gfoudree/TOTPVault/totpvault-cli/src/tests.rs

#[cfg(test)]
mod tests {
    use crate::comm::send_message;
    use crate::dev::DEFAULT_UART_DELAY;
    use crate::{comm::check_status_msg, dev::TotpvaultDev};
    use base64::Engine;
    use base64::prelude::BASE64_STANDARD;
    use chrono::Utc;
    use ed25519_dalek::{Signature, Signer, SigningKey, VerifyingKey};
    use rand_latest::Rng;
    use rand_older::rngs::OsRng;
    use rmp_serde::to_vec;
    use serial_test::serial;
    use std::time;
    use std::{env, thread, time::Duration};
    use totp_rs::{Secret, TOTP};
    use totpvault_lib::{
        AUTO_VAULT_LOCK_SECONDS, AUTOLOCK_OFF, AUTOLOCK_ON, AuthenticateChallengeMsg, CMD_ATTEST,
        CreateEntryMsg, MAX_PW_LEN, MSG_STATUS_MSG, Message, SETTING_AUTOLOCK, StatusMsg,
    };

    const TEST_PASSWORD: &str = "password12345!";

    fn init_vault(dev: &String) {
        let valid_pw = TEST_PASSWORD;
        TotpvaultDev::init_vault(&dev, None, valid_pw).unwrap();
    }
    fn unlock_vault(dev: &String) {
        let valid_pw = TEST_PASSWORD;
        TotpvaultDev::unlock_vault(&dev, None, valid_pw).unwrap();
    }

    #[test]
    fn test_public_key_to_hash_invalid_base64() {
        let invalid_public_key = "!!invalid_base64!!";
        assert!(TotpvaultDev::public_key_to_hash(invalid_public_key).is_err());
    }

    #[test]
    fn test_public_key_to_hash_empty_input() {
        let empty_key = "";
        assert!(TotpvaultDev::public_key_to_hash(empty_key).is_err());
    }
    #[test]
    fn test_public_key_to_hash_valid_input() {
        let valid_key = "U29tZVZhbGlkUHVibGljS2V5";
        assert!(TotpvaultDev::public_key_to_hash(valid_key).is_ok());
    }

    #[test]
    fn test_valid_signature() {
        // Generate a signing key
        let mut csprng = OsRng;
        let signing_key = SigningKey::generate(&mut csprng);
        let verifying_key = VerifyingKey::from(&signing_key);

        let message = b"Hello, world!";
        let signature: Signature = signing_key.sign(message);

        // Verify the signature
        let result = TotpvaultDev::ed25519_verify_signature(
            verifying_key.as_bytes(),
            message,
            &signature.to_vec(),
        );

        assert!(result.is_ok());
    }

    #[test]
    fn test_invalid_signature() {
        let mut csprng = OsRng;
        let signing_key = SigningKey::generate(&mut csprng);
        let verifying_key = VerifyingKey::from(&signing_key);

        let message = b"Hello, world!";
        let signature: Signature = signing_key.sign(message);

        // Tampered message
        let tampered_message = b"Hello, rust!";

        let result = TotpvaultDev::ed25519_verify_signature(
            verifying_key.as_bytes(),
            tampered_message,
            &signature.to_vec(),
        );

        assert!(result.is_err());
    }

    #[test]
    fn test_invalid_public_key() {
        let mut csprng = OsRng;
        let signing_key = SigningKey::generate(&mut csprng);

        let message = b"Hello, world!";
        let signature: Signature = signing_key.sign(message);

        // Generate a different keypair
        let different_signing_key = SigningKey::generate(&mut csprng);
        let different_verifying_key = VerifyingKey::from(&different_signing_key);

        let result = TotpvaultDev::ed25519_verify_signature(
            different_verifying_key.as_bytes(),
            message,
            &signature.to_vec(),
        );

        assert!(result.is_err());
    }

    #[test]
    fn test_empty_fields() {
        let empty_field = [0u8; 32];
        let mut csprng = OsRng;
        let signing_key = SigningKey::generate(&mut csprng);
        let verifying_key = VerifyingKey::from(&signing_key);

        let message = b"Hello, world!";
        let signature: Signature = signing_key.sign(message);

        assert!(
            TotpvaultDev::ed25519_verify_signature(
                verifying_key.as_bytes(),
                &empty_field,
                &signature.to_vec()
            )
            .is_err()
        );
        assert!(
            TotpvaultDev::ed25519_verify_signature(&empty_field, message, &signature.to_vec())
                .is_err()
        );
        assert!(
            TotpvaultDev::ed25519_verify_signature(verifying_key.as_bytes(), message, &empty_field)
                .is_err()
        );
    }

    #[test]
    fn test_valid_success_status_msg() {
        let status_msg = StatusMsg {
            error: false,
            message: "Operation successful".to_string(),
        };
        let mut encoded = vec![MSG_STATUS_MSG];
        encoded.extend(to_vec(&status_msg).unwrap());

        let result = check_status_msg(encoded);
        assert!(result.is_ok());
    }

    #[test]
    fn test_valid_error_status_msg() {
        let status_msg = StatusMsg {
            error: true,
            message: "Something went wrong".to_string(),
        };
        let mut encoded = vec![MSG_STATUS_MSG];
        encoded.extend(to_vec(&status_msg).unwrap());

        let result = check_status_msg(encoded);
        assert_eq!(result, Err("Something went wrong".to_string()));
    }

    #[test]
    fn test_invalid_message_type() {
        let invalid_type = 2; // Some other message type
        let status_msg = StatusMsg {
            error: false,
            message: "This should be ignored".to_string(),
        };
        let mut encoded = vec![invalid_type];
        encoded.extend(to_vec(&status_msg).unwrap());

        let result = check_status_msg(encoded);
        assert!(result.is_err());
        assert!(
            result
                .unwrap_err()
                .contains("Got unexpected message, type: 2")
        );
    }

    #[test]
    fn test_malformed_message() {
        let mut invalid_data = vec![MSG_STATUS_MSG];
        invalid_data.extend(vec![0, 1, 2, 3, 4]); // Corrupt data

        let result = check_status_msg(invalid_data);
        assert!(result.is_err());
        assert!(
            result
                .unwrap_err()
                .contains("Error deserializing StatusMsg")
        );
    }

    #[test]
    fn test_empty_message() {
        let result = check_status_msg(vec![]);
        assert!(result.is_err()); // Should fail due to missing type byte
    }

    #[test]
    fn test_message_with_only_type_byte() {
        let result = check_status_msg(vec![MSG_STATUS_MSG]);
        assert!(result.is_err()); // Should fail due to missing payload
    }

    #[test]
    fn test_totp_validation_algorithm() {
        for _ in 0..2048 {
            let secret = Secret::generate_secret();
            let b32_encoded_secret = secret.to_encoded().to_string();

            let create_msg = CreateEntryMsg {
                domain_name: "google.com".to_string(),
                totp_secret: b32_encoded_secret,
            };
            assert_eq!(create_msg.validate(), true);
        }
    }

    // Hardware tests
    #[test]
    #[serial]
    fn test_hw_autolock() {
        // Let the port be specified as an env variable
        let dev = match env::var("ESP_PORT") {
            Ok(user_provided_port) => user_provided_port,
            Err(_) => TotpvaultDev::find_device().unwrap(),
        };

        // Create with valid password
        init_vault(&dev);

        TotpvaultDev::unlock_vault(&dev, None, TEST_PASSWORD).unwrap();

        // Set autolock off to test
        TotpvaultDev::set_setting(&dev, None, SETTING_AUTOLOCK, "off").unwrap();
        let settings = TotpvaultDev::get_all_settings(&dev, None).unwrap();
        assert!(settings.get(SETTING_AUTOLOCK).unwrap() == AUTOLOCK_OFF);

        println!("Waiting {AUTO_VAULT_LOCK_SECONDS} seconds to make sure vault does not lock...");
        thread::sleep(time::Duration::from_secs(AUTO_VAULT_LOCK_SECONDS + 5));
        assert!(TotpvaultDev::list_stored_credentials(&dev, None).is_ok()); // Make sure it didn't lock on us
        assert!(
            TotpvaultDev::get_device_status(&dev, None)
                .unwrap()
                .vault_unlocked
                == true
        );

        // Set autolock timer
        TotpvaultDev::set_setting(&dev, None, SETTING_AUTOLOCK, "on").unwrap();

        // Check that setting worked
        assert!(
            TotpvaultDev::get_all_settings(&dev, None)
                .unwrap()
                .get(SETTING_AUTOLOCK)
                .unwrap()
                == AUTOLOCK_ON
        );
        // Wait again...
        thread::sleep(time::Duration::from_secs(AUTO_VAULT_LOCK_SECONDS + 5));
        assert!(
            TotpvaultDev::get_device_status(&dev, None)
                .unwrap()
                .vault_unlocked
                == false
        );

        // Unlock vault so you can change the setting
        TotpvaultDev::unlock_vault(&dev, None, TEST_PASSWORD).unwrap();

        // Disable autolock timer and wait again...
        TotpvaultDev::set_setting(&dev, None, SETTING_AUTOLOCK, "off").unwrap();
        // Vault should still be locked

        // Now wait to make sure it doesn't unlock itself
        TotpvaultDev::unlock_vault(&dev, None, TEST_PASSWORD).unwrap();

        assert!(
            TotpvaultDev::get_device_status(&dev, None)
                .unwrap()
                .vault_unlocked
                == true
        );

        thread::sleep(time::Duration::from_secs(AUTO_VAULT_LOCK_SECONDS + 5));

        assert!(
            TotpvaultDev::get_device_status(&dev, None)
                .unwrap()
                .vault_unlocked
                == true
        );
    }

    #[test]
    #[serial]
    fn test_hw_init_vault() {
        let valid_totp_secret = "HVR4CFHAFOWFGGFAGSA5JVTIMMPG6GMT";

        // Let the port be specified as an env variable
        let dev = match env::var("ESP_PORT") {
            Ok(user_provided_port) => user_provided_port,
            Err(_) => TotpvaultDev::find_device().unwrap(),
        };

        // Test with invalid password
        assert!(TotpvaultDev::init_vault(&dev, None, "pass").is_err());
        assert!(TotpvaultDev::init_vault(&dev, None, "").is_err());
        assert!(
            TotpvaultDev::init_vault(&dev, None, "a".repeat(MAX_PW_LEN + 10).as_str()).is_err()
        );

        // Create with valid password
        init_vault(&dev);

        println!("Vault initialized... Testing blocked options");

        // Check that all options are blocked when the vault is locked
        assert!(TotpvaultDev::list_stored_credentials(&dev, None).is_err());
        assert!(TotpvaultDev::add_credential(&dev, None, "google.com", valid_totp_secret).is_err());
        assert!(TotpvaultDev::sync_time(&dev, None).is_err());
        assert!(TotpvaultDev::delete_credential(&dev, None, "google.com").is_err());
        assert!(TotpvaultDev::get_totp_code(&dev, None, "google.com").is_err());

        // Check that specific options are allowed even if it's locked: Status
        let mut status = TotpvaultDev::get_device_status(&dev, None).unwrap();
        assert_eq!(status.vault_unlocked, false);

        // Check that slot usage is correct after formatting (used/free is hidden if locked)
        assert_eq!(status.used_slots, 0);
        assert_eq!(status.free_slots, 0);
        assert_eq!(status.total_slots, 64);
        assert!(status.public_key.len() > 16);
        assert!(status.version_str.contains("Version"));
        assert!(status.current_timestamp > 1);

        println!("Testing vault locking and status");
        // Unlock vault
        assert!(TotpvaultDev::unlock_vault(&dev, None, "pass").is_err());
        assert!(TotpvaultDev::unlock_vault(&dev, None, "").is_err());
        assert!(TotpvaultDev::unlock_vault(&dev, None, "\x00").is_err());
        assert!(
            TotpvaultDev::unlock_vault(&dev, None, "a".repeat(MAX_PW_LEN + 10).as_str()).is_err()
        );

        TotpvaultDev::unlock_vault(&dev, None, TEST_PASSWORD).unwrap();
        status = TotpvaultDev::get_device_status(&dev, None).unwrap();
        assert_eq!(status.vault_unlocked, true);
        assert_eq!(status.used_slots, 0);
        assert_eq!(status.free_slots, 64);
        assert_eq!(status.total_slots, status.free_slots);
        assert!(status.public_key.len() > 16);
        assert!(status.version_str.contains("Version"));
        assert!(status.current_timestamp > 1);

        // Test lock -> unlock
        TotpvaultDev::lock_vault(&dev, None).unwrap();
        status = TotpvaultDev::get_device_status(&dev, None).unwrap();
        assert_eq!(status.vault_unlocked, false);

        unlock_vault(&dev);

        status = TotpvaultDev::get_device_status(&dev, None).unwrap();
        assert_eq!(status.vault_unlocked, true);

        // Sync time
        TotpvaultDev::sync_time(&dev, None).unwrap();

        println!("Testing creation of invalid items");
        // Test creating invalid items
        assert!(
            TotpvaultDev::list_stored_credentials(&dev, None)
                .unwrap()
                .is_empty()
        );
        assert!(TotpvaultDev::add_credential(&dev, None, "g", valid_totp_secret).is_err());
        assert!(
            TotpvaultDev::add_credential(&dev, None, "g".repeat(512).as_str(), valid_totp_secret)
                .is_err()
        );
        assert!(TotpvaultDev::add_credential(&dev, None, "", valid_totp_secret).is_err());
        assert!(TotpvaultDev::add_credential(&dev, None, "google.com", "").is_err());
        assert!(
            TotpvaultDev::add_credential(&dev, None, "google.com", "a".repeat(512).as_str())
                .is_err()
        );
        assert!(
            TotpvaultDev::list_stored_credentials(&dev, None)
                .unwrap()
                .is_empty()
        );

        println!("Testing creation of valid items");
        // Make valid items
        for i in 0..64 {
            let domain = format!("test{}.com", i as u8);
            println!("{}", domain);
            TotpvaultDev::add_credential(&dev, None, domain.as_str(), valid_totp_secret).unwrap();
            let creds = TotpvaultDev::list_stored_credentials(&dev, None).unwrap();
            assert_eq!(creds.len(), i + 1);
            status = TotpvaultDev::get_device_status(&dev, None).unwrap();
            assert_eq!(status.used_slots, i as u8 + 1);
            assert_eq!(status.free_slots, 64 - (i as u8 + 1));
        }

        print!("Testing deleting items");

        // Test adding duplicate entries
        assert!(TotpvaultDev::add_credential(&dev, None, "test0.com", valid_totp_secret).is_err());

        // Test deleting entries
        {
            TotpvaultDev::delete_credential(&dev, None, "test0.com").unwrap();
            // Check that test0.com is gone
            let post_delete_creds = TotpvaultDev::list_stored_credentials(&dev, None).unwrap();
            for cred in post_delete_creds {
                assert_ne!(cred.domain_name, "test0.com");
            }
            // Check if we try and delete a non-existent entry
            assert!(TotpvaultDev::delete_credential(&dev, None, "test0.com").is_err());
            assert!(TotpvaultDev::get_totp_code(&dev, None, "test0.com").is_err());
            // Check that we can add it again
            TotpvaultDev::add_credential(&dev, None, "test0.com", valid_totp_secret).unwrap();
            TotpvaultDev::get_totp_code(&dev, None, "test0.com").unwrap();
        }

        // Now the device is full, make sure adding an item fails
        assert!(
            TotpvaultDev::add_credential(&dev, None, "test_too_full.com", valid_totp_secret)
                .is_err()
        );
    }

    #[test]
    #[serial]
    fn test_hw_attestation() {
        // Let the port be specified as an env variable
        let dev = match env::var("ESP_PORT") {
            Ok(user_provided_port) => user_provided_port,
            Err(_) => TotpvaultDev::find_device().unwrap(),
        };

        init_vault(&dev);
        unlock_vault(&dev);
        // Sync time
        TotpvaultDev::sync_time(&dev, None).unwrap();

        // Test too short of a public key
        let test_pub_key = [1u8; 16]; // Too short
        let pub_key_b64 = BASE64_STANDARD.encode(&test_pub_key);
        let result = TotpvaultDev::attest_device(dev.as_str(), None, &pub_key_b64);
        assert!(result.is_err());

        // Test too short challenges
        for c in [0, 1, 10] {
            let mut random_bytes = Vec::with_capacity(c);
            rand_latest::fill(random_bytes.as_mut_slice());

            let random_bytes_encoded = BASE64_STANDARD.encode(&random_bytes);

            assert!(
                send_message(
                    dev.as_str(),
                    AuthenticateChallengeMsg {
                        nonce_challenge: random_bytes_encoded
                    },
                    CMD_ATTEST,
                    DEFAULT_UART_DELAY
                )
                .is_err()
            );
        }

        // Test with incorrect public key
        let incorrect_public_key = "1EfTKDTSnPWohuhbddiruUbIaZcgou5YPYMDR2lW94Q=";
        assert!(TotpvaultDev::attest_device(&dev, None, &incorrect_public_key).is_err());

        // Test with correct public key
        let correct_public_key = TotpvaultDev::get_device_status(&dev, None)
            .unwrap()
            .public_key;
        TotpvaultDev::attest_device(&dev, None, &correct_public_key).unwrap();
    }
    #[test]
    #[serial]
    fn test_hw_totp_code() {
        // Let the port be specified as an env variable
        let dev = match env::var("ESP_PORT") {
            Ok(user_provided_port) => user_provided_port,
            Err(_) => TotpvaultDev::find_device().unwrap(),
        };

        init_vault(&dev);
        unlock_vault(&dev);
        // Sync time
        TotpvaultDev::sync_time(&dev, None).unwrap();
        assert!(
            TotpvaultDev::list_stored_credentials(&dev, None)
                .unwrap()
                .is_empty()
        );

        // First phase: Create all credential entries
        let mut credentials = Vec::with_capacity(25);
        for i in 0..25 {
            let secret = Secret::generate_secret();
            let b32_encoded_secret = secret.to_encoded().to_string();
            let domain_name = format!("test{}.com", i);

            // Add it to the vault
            TotpvaultDev::add_credential(
                &dev,
                None,
                domain_name.as_str(),
                b32_encoded_secret.as_str(),
            )
            .unwrap();

            // Store the domain and secret for later verification
            println!("Adding {}: {}", domain_name, b32_encoded_secret);
            credentials.push((domain_name, secret));
        }

        println!("Adding entries complete!");
        // Second phase: Retrieve and verify TOTP codes with random delays
        let mut rng = rand_latest::rng();

        // 50 passes of checking TOTP codes
        for i in 0..50 {
            // Random delay between 1 and 35 seconds to catch window rollovers
            let delay_seconds = rng.random_range(1..=35);
            println!(
                "[Pass {}]: Waiting for {} seconds before checking",
                i, delay_seconds
            );
            thread::sleep(Duration::from_secs(delay_seconds));
            for (domain_name, secret) in &credentials {
                // Retrieve TOTP code from the hardware device
                let mut retrieved_totp_code =
                    TotpvaultDev::get_totp_code(&dev, None, domain_name.as_str()).unwrap();

                // Check if we are out-of-sync and fix if needed
                if ((Utc::now().timestamp() as u64 - retrieved_totp_code.system_timestamp) as i64)
                    .abs()
                    > 1
                {
                    println!("Time out of sync, re-syncing for {}", domain_name);
                    TotpvaultDev::sync_time(&dev, None).unwrap(); // Sync time
                    retrieved_totp_code =
                        TotpvaultDev::get_totp_code(&dev, None, domain_name.as_str()).unwrap(); // Get new value
                }

                // Generate expected TOTP code
                let totp = TOTP::new(
                    totp_rs::Algorithm::SHA1,
                    6,
                    1,
                    30,
                    secret.to_bytes().unwrap(),
                )
                .unwrap();
                let mut expected_code = totp.generate_current().unwrap();

                // Verify the TOTP code. If not equal, wait a second and try again to handle window boundry
                if expected_code != retrieved_totp_code.totp_code {
                    thread::sleep(Duration::from_secs(2));
                    retrieved_totp_code =
                        TotpvaultDev::get_totp_code(&dev, None, domain_name.as_str()).unwrap();
                    expected_code = totp.generate_current().unwrap();

                    if expected_code != retrieved_totp_code.totp_code {
                        println!("{}", domain_name);
                        assert_eq!(expected_code, retrieved_totp_code.totp_code); // Fail if it's wrong again
                    }
                }
            }
        }
    }
}
